DarrenProng/Hardware-Production/images/20181120_174603.jpg

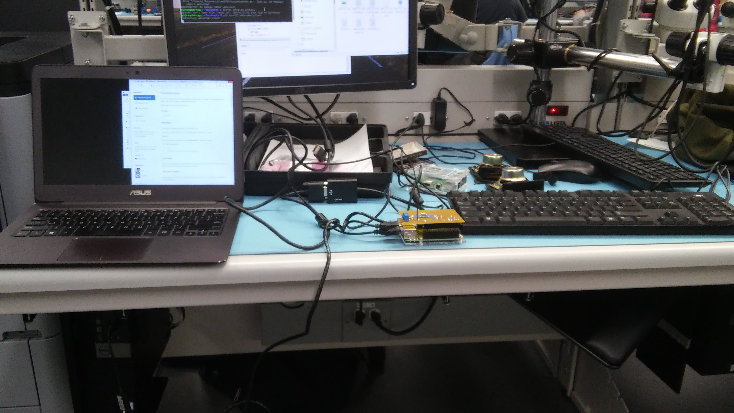
images/20181120_174603.jpg
