DarrenProng/Hardware-Production/images/Enclosure_Prototype.jpg

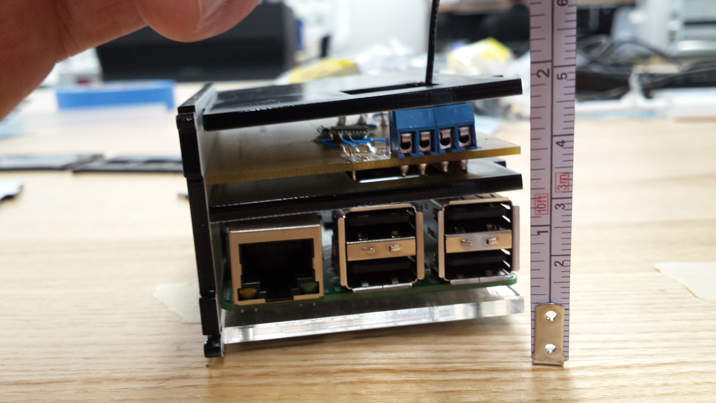
images/Enclosure_Prototype.jpg
