DarrenProng/Hardware-Production/images/LCM386_amplifier.jpg

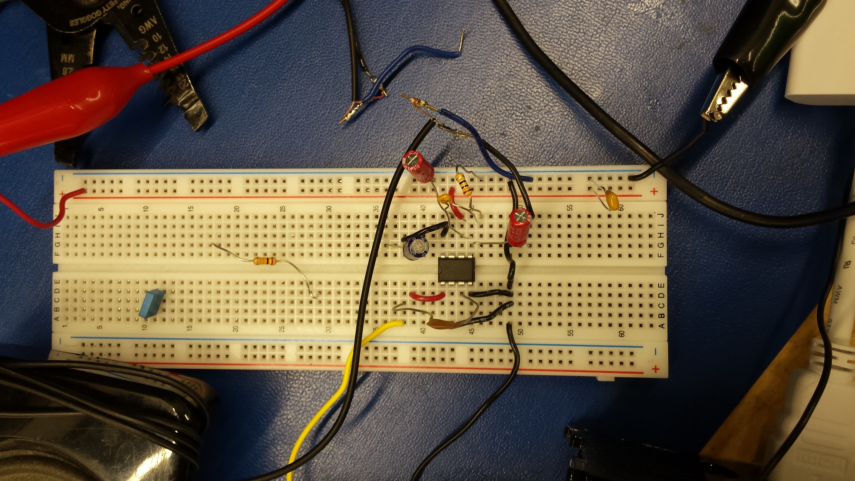
images/LCM386_amplifier.jpg
