DarrenProng/Hardware-Production/images/MiddlePlate.jpg

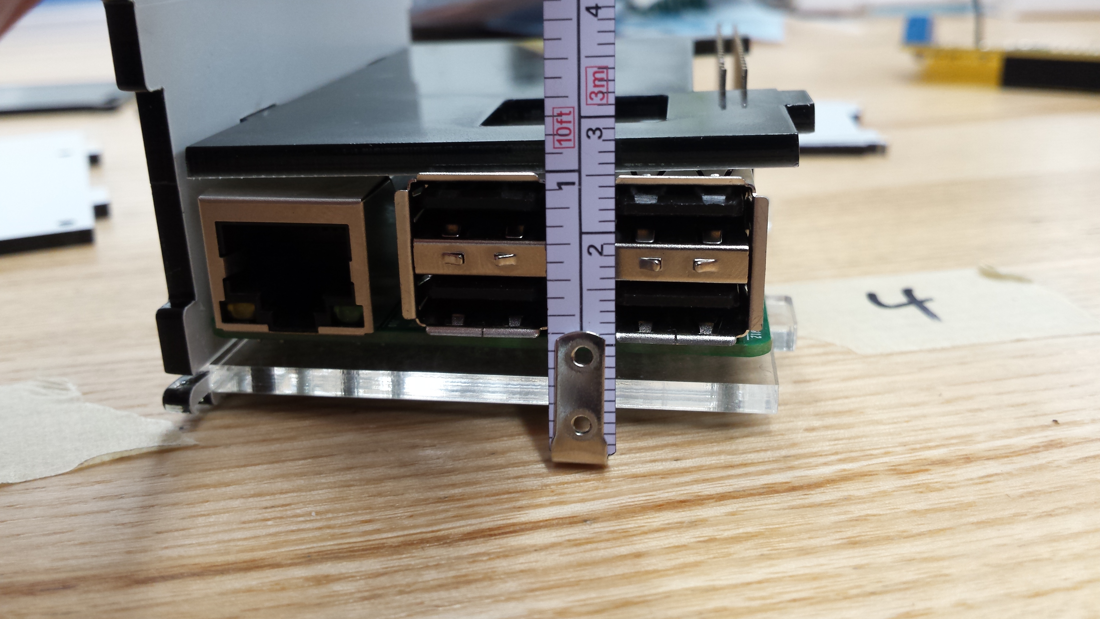
images/MiddlePlate.jpg
