DarrenProng/Hardware-Production/images/PCB.png

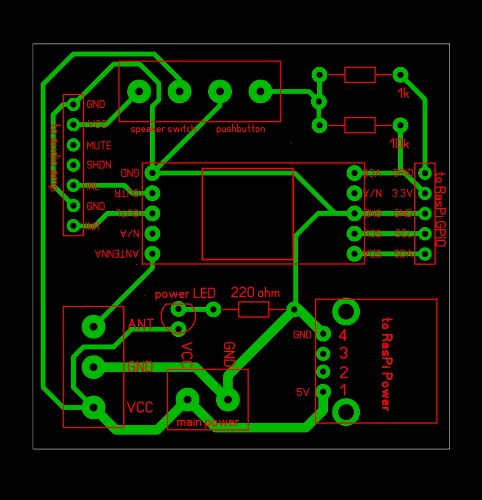
images/PCB.png
