DarrenProng/Hardware-Production/images/PI_GPIOPanel.JPG

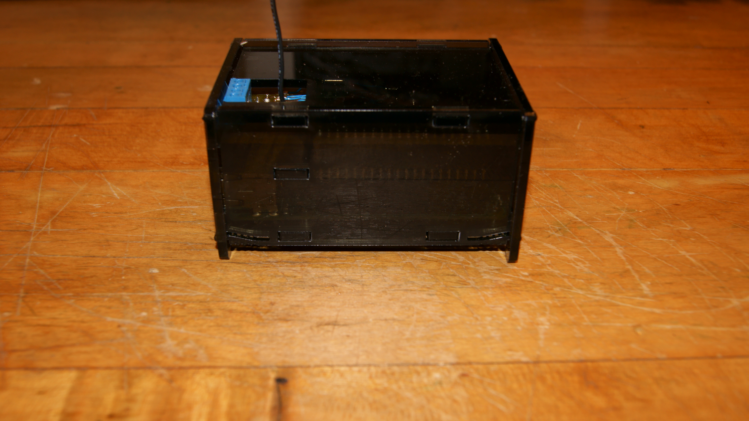
images/PI_GPIOPanel.JPG
