DarrenProng/Hardware-Production/images/PI_PluggedIn.jpg

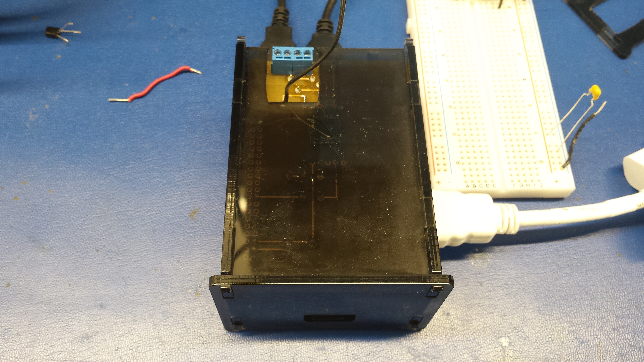
images/PI_PluggedIn.jpg
