DarrenProng/Hardware-Production/images/ShippingPackage.jpg

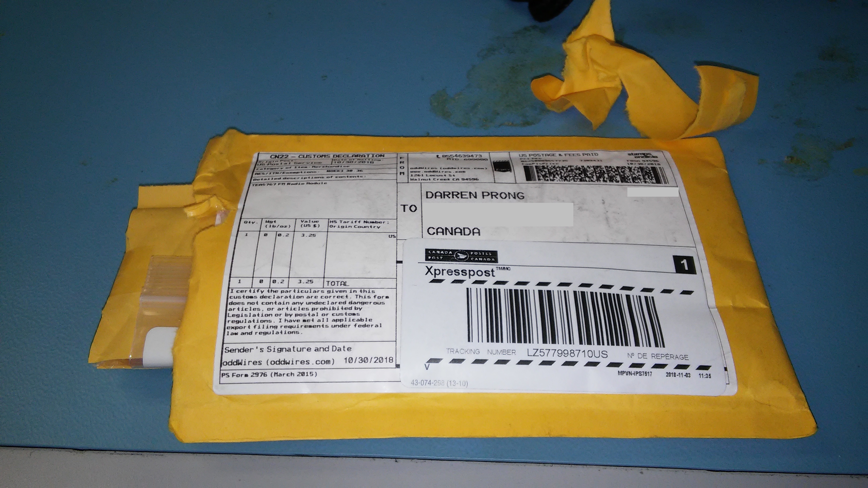
images/ShippingPackage.jpg
