DarrenProng/Hardware-Production/images/StackableHeader_RaspberryPI.jpg

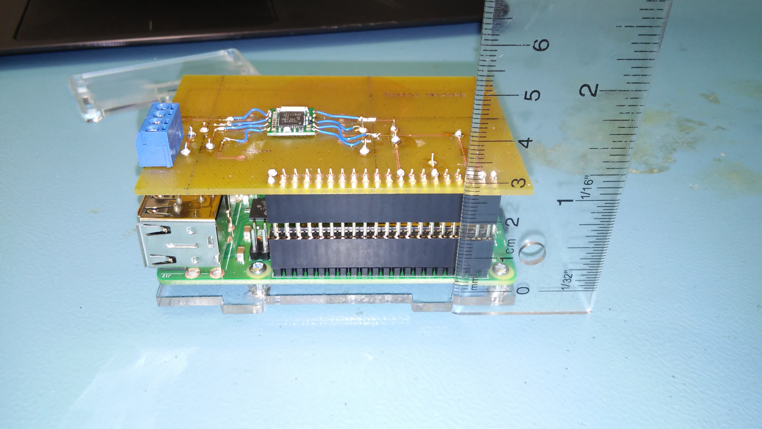
images/StackableHeader_RaspberryPI.jpg
